AnotherJohnH/picoX7/Source/DX7/OpsAlg6.h

//------------------------------------------------------------------------------
// The data in this file is a derivative of data reverse engineered from die
// photographs of the YM21280 published in Ken Shirriff's blog. That publicly
// available document does not contain a copyright notice or any mention of
// permissions or restrictions that apply to the use of the data. However,
// according to law that does not necessarily mean that the data is free from
// restrictions on its use. At the time of publication, the copyright holder
// is probably Yamaha. If the copyright holder wishes to retrospectively declare
// reasonable and legal restrictions on the data, then either those restrictions
// must be obeyed or this file shouled be deleted.
//
// The statements above shall be included in all copies or substantial portions
// of the data.
//
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
// \brief OPS YM21280 Algorithm
//
// Credit to Ken Shirriff for his decode of the algorithm ROM in the YM21280
// via decapping and die photography

#pragma once

#include "Ops.h"

namespace DX {

//! Implement the 32 DX7 OP algorithms in the YM21280 OPS
template <typename EG_TYPE>
class OpsAlg6 : public Ops</* NUM_OP */ 6, EG_TYPE>
{
public:
   OpsAlg6() = default;

   //! Return next sample for the selected algorithm
   int32_t operator()()
   {
      return (this->*alg_ptr)();
   }

   //! Set the algorithm
   void setOpsAlg(uint8_t algorithm)
   {
      switch (algorithm + 1)
      {
      case  1: alg_ptr = &OpsAlg6::alg1;  break;
      case  2: alg_ptr = &OpsAlg6::alg2;  break;
      case  3: alg_ptr = &OpsAlg6::alg3;  break;
      case  4: alg_ptr = &OpsAlg6::alg4;  break;
      case  5: alg_ptr = &OpsAlg6::alg5;  break;
      case  6: alg_ptr = &OpsAlg6::alg6;  break;
      case  7: alg_ptr = &OpsAlg6::alg7;  break;
      case  8: alg_ptr = &OpsAlg6::alg8;  break;
      case  9: alg_ptr = &OpsAlg6::alg9;  break;
      case 10: alg_ptr = &OpsAlg6::alg10; break;
      case 11: alg_ptr = &OpsAlg6::alg11; break;
      case 12: alg_ptr = &OpsAlg6::alg12; break;
      case 13: alg_ptr = &OpsAlg6::alg13; break;
      case 14: alg_ptr = &OpsAlg6::alg14; break;
      case 15: alg_ptr = &OpsAlg6::alg15; break;
      case 16: alg_ptr = &OpsAlg6::alg16; break;
      case 17: alg_ptr = &OpsAlg6::alg17; break;
      case 18: alg_ptr = &OpsAlg6::alg18; break;
      case 19: alg_ptr = &OpsAlg6::alg19; break;
      case 20: alg_ptr = &OpsAlg6::alg20; break;
      case 21: alg_ptr = &OpsAlg6::alg21; break;
      case 22: alg_ptr = &OpsAlg6::alg22; break;
      case 23: alg_ptr = &OpsAlg6::alg23; break;
      case 24: alg_ptr = &OpsAlg6::alg24; break;
      case 25: alg_ptr = &OpsAlg6::alg25; break;
      case 26: alg_ptr = &OpsAlg6::alg26; break;
      case 27: alg_ptr = &OpsAlg6::alg27; break;
      case 28: alg_ptr = &OpsAlg6::alg28; break;
      case 29: alg_ptr = &OpsAlg6::alg29; break;
      case 30: alg_ptr = &OpsAlg6::alg30; break;
      case 31: alg_ptr = &OpsAlg6::alg31; break;
      case 32: alg_ptr = &OpsAlg6::alg32; break;
      }
   }

private:
   int32_t alg1()
   {
      (void) this->template ops<6, /* SEL */ 1, /* A */ 1, /* C */ 0, /* D */ 0, /* LOG2_COM */ 0b00000>();
      (void) this->template ops<5, /* SEL */ 1, /* A */ 0, /* C */ 0, /* D */ 0, /* LOG2_COM */ 0b00000>();
      (void) this->template ops<4, /* SEL */ 1, /* A */ 0, /* C */ 0, /* D */ 0, /* LOG2_COM */ 0b00000>();
      (void) this->template ops<3, /* SEL */ 0, /* A */ 0, /* C */ 0, /* D */ 1, /* LOG2_COM */ 0b01000>();
      (void) this->template ops<2, /* SEL */ 1, /* A */ 0, /* C */ 1, /* D */ 0, /* LOG2_COM */ 0b00000>();
      return this->template ops<1, /* SEL */ 5, /* A */ 0, /* C */ 1, /* D */ 1, /* LOG2_COM */ 0b01000>();
   }

   int32_t alg2()
   {
      (void) this->template ops<6, /* SEL */ 1, /* A */ 0, /* C */ 0, /* D */ 0, /* LOG2_COM */ 0b00000>();
      (void) this->template ops<5, /* SEL */ 1, /* A */ 0, /* C */ 0, /* D */ 0, /* LOG2_COM */ 0b00000>();
      (void) this->template ops<4, /* SEL */ 1, /* A */ 0, /* C */ 0, /* D */ 0, /* LOG2_COM */ 0b00000>();
      (void) this->template ops<3, /* SEL */ 5, /* A */ 0, /* C */ 0, /* D */ 1, /* LOG2_COM */ 0b01000>();
      (void) this->template ops<2, /* SEL */ 1, /* A */ 1, /* C */ 1, /* D */ 0, /* LOG2_COM */ 0b00000>();
      return this->template ops<1, /* SEL */ 0, /* A */ 0, /* C */ 1, /* D */ 1, /* LOG2_COM */ 0b01000>();
   }

   int32_t alg3()
   {
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
      (void) this->template ops<2, /* SEL */ 0, /* A */ 0, /* C */ 1, /* D */ 1, /* LOG2_COM */ 0b10101>();
      return this->template ops<1, /* SEL */ 5, /* A */ 0, /* C */ 1, /* D */ 1, /* LOG2_COM */ 0b10101>();
   }

   int32_t (OpsAlg6::*alg_ptr)() {&OpsAlg6::alg1};
};

} // namespace DX
