AnotherJohnH/picoX7/Source/DX7/DX7Firmware.h

//------------------------------------------------------------------------------
// The data in this file is a derivative of data reverse engineered from the
// DX7 firmware ROM published on AJXS github project. That publicly
// available project does not contain a copyright notice or any mention of
// permissions or restrictions that apply to the use of the data. However,
// according to law that does not necessarily mean that the data is free from
// restrictions on its use. At the time of publication, the copyright holder
// is probably Yamaha. If the copyright holder wishes to retrospectively declare
// reasonable and legal restrictions on the data, then either those restrictions
// must be obeyed or this file shouled be deleted.
//
// The statements above shall be included in all copies or substantial portions
// of the data.
//
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
// \brief DX7 firmware simulation
//
// Credit to AJXS for his excellent disassembly of the DX7 firmware ROM

#pragma once

#include "Egs.h"

#include "Lfo.h"
#include "Modulation.h"
#include "PitchEg.h"

namespace DX7 {

//! Model of Yamaha DX7 firmware
class Firmware
{
public:
   Firmware(Egs& hw_)
      : hw(hw_)
   {
   }

   //! Load voice patch
   void loadVoice(const SysEx::Voice* patch_)
   {
      voice_patch = *patch_;

      for(unsigned i = 0; i < SysEx::NUM_OP; i++)
      {
         const SysEx::Op& op = voice_patch.op[i];

         patchActivateOperatorEgRate(i, op);
         patchActivateOperatorEgLevel(i, op);
         patchActivateOperatorKbdScaling(i, op);
         patchActivateOperatorKbdVelSens(i, op);
         patchActivateOperatorPitch(i, op);
         patchActivateOperatorKbdRateScaling(i, op);
         patchActivateOperatorDetune(i, op);

         op_enable[i] = (patch_->operator_on & (1 << i)) != 0;
      }

      pitch_eg.load(voice_patch);
      patchActivateAlgMode();
      lfo.load(voice_patch);
   }

   //! Load param patch
   void loadParam(const SysEx::Param* patch_)
   {
      param_patch = *patch_;

      modulation.load(param_patch);
   }

   //! Implement HANDLER_OCF should be called 375 Hz
   void tick()
   {
      lfo.tick();

      computeAmplitudeModulation();

      if (pitch_eg.tick())
      {
         voiceAddLoadFreqToEgs(key_pitch);
      }

      computePitchModulation();

      hw.sendEgsFreq();
   }

   //! Implement VOICE_ADD called for a note on event
   void voiceAdd(uint8_t note_, uint8_t midi_velocity_)
   {
      static const uint8_t table_midi_vel[32] =
      {
         0x6E, 0x64, 0x5A, 0x55, 0x50, 0x4B, 0x46, 0x41,
         0x3A, 0x36, 0x32, 0x2E, 0x2A, 0x26, 0x22, 0x1E,
         0x1C, 0x1A, 0x18, 0x16, 0x14, 0x12, 0x10, 0x0E,
         0x0C, 0x0A, 0x08, 0x06, 0x04, 0x02, 0x01, 0x00
      };

      uint8_t velocity = table_midi_vel[midi_velocity_ >> 2];

      uint8_t note = note_ + voice_patch.transpose - 24;
      if (note > 127)
         note = 127;

      key_pitch = voiceConvertNoteToLogFreq(note);

      voiceAddLoadOperatorDataToEgs(key_pitch, velocity);

      voiceAddLoadFreqToEgs(key_pitch);

      lfo.keyOn();
      pitch_eg.keyOn(/* voice */ 0);

      hw.sendEgsFreq();
      hw.keyOn();
   }

   //! Implement VOICE_REMOVE called for a note off event
   void voiceRemove()
   {
      pitch_eg.keyOff(/* voice */ 0);
      hw.keyOff();
   }

   //! Implement PITCH_BEND_PARSE
   void setPitchBend(int16_t raw14_) { pitch_bend = raw14_; }

   //! Set raw modulation input
   void setModWheel(        uint8_t raw_) { modulation.rawInput(Modulation::MOD_WHEEL,      raw_); }
   void setModFootControl(  uint8_t raw_) { modulation.rawInput(Modulation::FOOT_CONTROL,   raw_); }
   void setModBreathControl(uint8_t raw_) { modulation.rawInput(Modulation::BREATH_CONTROL, raw_); }
   void setModAfterTouch(   uint8_t raw_) { modulation.rawInput(Modulation::AFTER_TOUCH,    raw_); }

private:
   //! Implement PATCH_ACTIVATE_OPERATOR_EG_RATE
   void patchActivateOperatorEgRate(unsigned op_index_, const SysEx::Op& op_)
   {
      for(unsigned i = 0; i < 4; ++i)
      {
         uint8_t rate6 = (op_.eg_amp.rate[i] * 164) >> 8;

         hw.op[op_index_].setEgRate(i, rate6);
      }
   }

   //! Implement PATCH_ACTIVATE_OPERATOR_EG_LEVEL
   void patchActivateOperatorEgLevel(unsigned op_index_, const SysEx::Op& op_)
   {
      for(unsigned i = 0; i < 4; ++i)
      {
         uint8_t level6 = table_log[op_.eg_amp.level[i]] >> 1;

         hw.op[op_index_].setEgAtten(i, level6);
      }
   }

   //! Implement PATCH_ACTIVATE_OPERATOR_KBD_SCALING
   void patchActivateOperatorKbdScaling(unsigned index, const SysEx::Op& op)
   {
      unsigned breakpoint  = table_key_pitch[op.kbd_lvl_scl_bpt + 20] >> 2;
      unsigned depth_left  = (op.kbd_lvl_scl_lft_depth * 660) >> 8;
      unsigned depth_right = (op.kbd_lvl_scl_rgt_depth * 660) >> 8;

      static const uint8_t table_kbd_scaling_curve_exp[36] =
      {
         0x00, 0x01, 0x02, 0x03, 0x04, 0x05,
         0x06, 0x07, 0x08, 0x09, 0x0B, 0x0E,
         0x10, 0x13, 0x17, 0x1C, 0x21, 0x27,
         0x2F, 0x39, 0x43, 0x50, 0x5F, 0x71,
         0x86, 0xA0, 0xBE, 0xE0, 0xFF, 0xFF,
         0xFF, 0xFF, 0xFF, 0xFF, 0xFF, 0xFF
      };

      static const uint8_t table_kbd_scaling_curve_lin[36] =
      {
         0x00, 0x08, 0x10, 0x18, 0x20, 0x28,
         0x30, 0x38, 0x40, 0x48, 0x50, 0x58,
         0x60, 0x68, 0x70, 0x78, 0x80, 0x88,
         0x90, 0x98, 0xA0, 0xA8, 0xB2, 0xB8,
         0xC0, 0xC8, 0xD0, 0xD8, 0xE0, 0xE8,
         0xF0, 0xF8, 0xFF, 0xFF, 0xFF, 0xFF
      };

      // Note, sign is "opposite" as lower values are louder

      signed         left_sign  = op.kbd_lvl_scl_lft_curve >= 2 ? -1 : +1;
      bool           left_lin   = op.kbd_lvl_scl_lft_curve == 0 || op.kbd_lvl_scl_lft_curve == 3;
      const uint8_t* left_curve = left_lin ? table_kbd_scaling_curve_lin
                                           : table_kbd_scaling_curve_exp;

      signed         right_sign  = op.kbd_lvl_scl_rgt_curve >= 2 ? -1 : +1;
      bool           right_lin   = op.kbd_lvl_scl_rgt_curve == 0 || op.kbd_lvl_scl_rgt_curve == 3;
      const uint8_t* right_curve = right_lin ? table_kbd_scaling_curve_lin
                                             : table_kbd_scaling_curve_exp;

      unsigned out_level = table_log[op.out_level];

      for(signed note = 1; note <= 43; ++note)
      {
         signed offset = note - breakpoint;

         signed curve = offset <= 0 ? left_curve[-offset] * depth_left * left_sign
                                    : right_curve[offset] * depth_right * right_sign;

         signed note_level = (out_level + (curve >> 8)) << 1;

         if (note_level < 0)
            note_level = 0;
         else if (note_level > 0xFF)
            note_level = 0xFF;

         operator_keyboard_scaling[index][note - 1] = note_level;
      }
   }

   //! Implement PATCH_ACTIVATE_OPERATOR_VEL_SENS
   void patchActivateOperatorKbdVelSens(unsigned index, const SysEx::Op& op)
   {
      patch_op_sens[index] = (8 - op.key_vel_sense) * 0x1E0;
   }

   //! Implement PATCH_ACTIVATE_OPERATOR_PITCH
   void patchActivateOperatorPitch(unsigned index, const SysEx::Op& op)
   {
      if (op.osc_mode == SysEx::RATIO)
      {
         const uint16_t table_op_freq_coarse[32] =
         {
            0xF000, 0x0000, 0x1000, 0x195C, 0x2000, 0x2528, 0x295C, 0x2CEC,
            0x3000, 0x32B8, 0x3528, 0x375A, 0x395C, 0x3B34, 0x3CEC, 0x3E84,
            0x4000, 0x4168, 0x42B8, 0x43F8, 0x4528, 0x4648, 0x475A, 0x4860,
            0x495C, 0x4A4C, 0x4B34, 0x4C14, 0x4CEC, 0x4DBA, 0x4E84, 0x4F44
         };

         const uint16_t table_op_freq_fine[100] =
         {
            0x000, 0x03A, 0x075, 0x0AE, 0x0E7, 0x120, 0x158, 0x18F, 0x1C6, 0x1FD,
            0x233, 0x268, 0x29D, 0x2D2, 0x306, 0x339, 0x36D, 0x39F, 0x3D2, 0x403,
            0x435, 0x466, 0x497, 0x4C7, 0x4F7, 0x526, 0x555, 0x584, 0x5B2, 0x5E0,
            0x60E, 0x63B, 0x668, 0x695, 0x6C1, 0x6ED, 0x719, 0x744, 0x76F, 0x799,
            0x7C4, 0x7EE, 0x818, 0x841, 0x86A, 0x893, 0x8BC, 0x8E4, 0x90C, 0x934,
            0x95C, 0x983, 0x9AA, 0x9D1, 0x9F7, 0xA1D, 0xA43, 0xA69, 0xA8F, 0xAB4,
            0xAD9, 0xAFE, 0xB22, 0xB47, 0xB6B, 0xB8F, 0xBB2, 0xBD6, 0xBF9, 0xC1C,
            0xC3F, 0xC62, 0xC84, 0xCA7, 0xCC9, 0xCEA, 0xD0C, 0xD2E, 0xD4F, 0xD70,
            0xD91, 0xDB2, 0xDD2, 0xDF3, 0xE13, 0xE33, 0xE53, 0xE72, 0xE92, 0xEB1,
            0xED0, 0xEEF, 0xF0E, 0xF2D, 0xF4C, 0xF6A, 0xF88, 0xFA6, 0xFC4, 0xFE2
         };

         hw.op[index].setPitchFixed(false);

         hw.op[index].setPitchRatio(table_op_freq_coarse[op.osc_freq_coarse] +
                                    table_op_freq_fine[op.osc_freq_fine] +
                                    0x232C);
      }
      else
      {
         const uint16_t table_op_freq_fixed[4] =
         {
            0x0000, 0x3526, 0x6A4C, 0x9F74
         };

         hw.op[index].setPitchFixed(true);

         hw.op[index].setPitchRatio(table_op_freq_fixed[op.osc_freq_coarse & 0b11] +
                                    op.osc_freq_fine * 136 +
                                    0x16AC);
      }
   }

   //! Implement PATCH_ACTIVATE_OPERATOR_KBD_RATE_SCALING
   void patchActivateOperatorKbdRateScaling(unsigned index, const SysEx::Op& op)
   {
      hw.op[index].setEgRateScale(op.kbd_rate_scale);
      hw.op[index].setAmpModSens(op.amp_mod_sense);
   }

   //! Implement PATCH_ACTIVATE_OPERATOR_DETUNE
   void patchActivateOperatorDetune(unsigned index, const SysEx::Op& op)
   {
      hw.op[index].setDetune(op.osc_detune - 7);
   }

   //! Implement PATCH_ACTIVATE_ALG_MODE
   void patchActivateAlgMode()
   {
      hw.setOpsSync(voice_patch.osc_sync);
      hw.setOpsAlg(voice_patch.alg);
      hw.setOpsFdbk(voice_patch.feedback);
   }

   //! Implement VOICE_CONVERT_NOTE_TO_LOG_FREQ
   uint16_t voiceConvertNoteToLogFreq(uint8_t note_)
   {
      uint8_t value   = table_key_pitch[note_];
      uint8_t ls_bits = value & 0b11;
      return (value << 8) | (ls_bits << 6) | (ls_bits << 4) | (ls_bits << 2);
   }

   //! Implement VOICE_ADD_LOAD_OPERATOR_DATA_TO_EGS
   void voiceAddLoadOperatorDataToEgs(uint16_t pitch_, uint8_t note_vel7_)
   {
      static uint8_t table_op_volume_velocity_scale[32] =
      {
         0x00, 0x04, 0x0C, 0x15, 0x1E, 0x28, 0x2E, 0x34,
         0x3A, 0x40, 0x46, 0x4C, 0x52, 0x58, 0x5E, 0x64,
         0x67, 0x6A, 0x6D, 0x70, 0x72, 0x74, 0x76, 0x78,
         0x7A, 0x7C, 0x7E, 0x80, 0x82, 0x83, 0x84, 0x85
      };

      uint8_t scale = table_op_volume_velocity_scale[note_vel7_ >> 2];

      for(unsigned op_index = 0; op_index < SysEx::NUM_OP; ++op_index)
      {
         uint16_t vel_sense = patch_op_sens[op_index];

         unsigned vol = ((vel_sense & 0xFF00) + scale * (vel_sense & 0xFF)) >> 8;
         if (vol > 0xFF) vol = 0xFF;

         op_volume[op_index] = vol;

         if (not op_enable[op_index])
         {
            vol = 0xFF;
         }
         else
         {
            vol = op_volume[op_index] + operator_keyboard_scaling[op_index][pitch_ >> 10];

            if (vol > 0xFF)
            {
               vol = 0xFF;
            }
            else if (vol < 4)
            {
               vol = 4;
            }
         }

         hw.op[op_index].setOpAtten(vol);
      }
   }

   //! Implement VOICE_ADD_LOAD_FREQ_TO_EGS
   void voiceAddLoadFreqToEgs(signed pitch_)
   {
      pitch_ += pitch_eg.getOutput(/* voice */ 0);

      pitch_ -= 0x1BA8;
      if (pitch_ < 0)
         pitch_ = 0;

      pitch_ += master_tune;

      hw.setEgsVoicePitch(pitch_);
   }

   void computeAmplitudeModulation()
   {
      unsigned mod = lfo.getAmpMod() + modulation.getAmpMod();
      if (mod > 0xFF) mod = 0xFF;

      mod += modulation.getEGBias();
      if (mod > 0xFF) mod = 0xFF;
      mod -= modulation.getEGBias();

      uint8_t value = (mod * (~lfo.getAmpOutput() ^ 0x80)) >> 8;
      value += modulation.getEGBias();
      if (value > 0xFF) value = 0xFF;

      static uint8_t table_amp_mod[256] =
      {
         0xFF, 0xFF, 0xE0, 0xCD, 0xC0, 0xB5, 0xAD, 0xA6, 0xA0, 0x9A, 0x95, 0x91, 0x8D, 0x89, 0x86, 0x82,
         0x80, 0x7D, 0x7A, 0x78, 0x75, 0x73, 0x71, 0x6F, 0x6D, 0x6B, 0x69, 0x67, 0x66, 0x64, 0x62, 0x61,
         0x60, 0x5E, 0x5D, 0x5B, 0x5A, 0x59, 0x58, 0x56, 0x55, 0x54, 0x53, 0x52, 0x51, 0x50, 0x4F, 0x4E,
         0x4D, 0x4C, 0x4B, 0x4A, 0x49, 0x48, 0x47, 0x46, 0x46, 0x45, 0x44, 0x43, 0x42, 0x42, 0x41, 0x40,
         0x40, 0x3F, 0x3E, 0x3D, 0x3D, 0x3C, 0x3B, 0x3B, 0x3A, 0x39, 0x39, 0x38, 0x38, 0x37, 0x36, 0x36,
         0x35, 0x35, 0x34, 0x33, 0x33, 0x32, 0x32, 0x31, 0x31, 0x30, 0x30, 0x2F, 0x2F, 0x2E, 0x2E, 0x2D,
         0x2D, 0x2C, 0x2C, 0x2B, 0x2B, 0x2A, 0x2A, 0x2A, 0x29, 0x29, 0x28, 0x28, 0x27, 0x27, 0x26, 0x26,
         0x26, 0x25, 0x25, 0x24, 0x24, 0x24, 0x23, 0x23, 0x22, 0x22, 0x22, 0x21, 0x21, 0x21, 0x20, 0x20,
         0x20, 0x1F, 0x1F, 0x1E, 0x1E, 0x1E, 0x1D, 0x1D, 0x1D, 0x1C, 0x1C, 0x1C, 0x1B, 0x1B, 0x1B, 0x1A,
         0x1A, 0x1A, 0x19, 0x19, 0x19, 0x18, 0x18, 0x18, 0x18, 0x17, 0x17, 0x17, 0x16, 0x16, 0x16, 0x15,
         0x15, 0x15, 0x15, 0x14, 0x14, 0x14, 0x13, 0x13, 0x13, 0x13, 0x12, 0x12, 0x12, 0x12, 0x11, 0x11,
         0x11, 0x11, 0x10, 0x10, 0x10, 0x10, 0x0F, 0x0F, 0x0F, 0x0F, 0x0E, 0x0E, 0x0E, 0x0E, 0x0D, 0x0D,
         0x0D, 0x0D, 0x0C, 0x0C, 0x0C, 0x0C, 0x0B, 0x0B, 0x0B, 0x0B, 0x0A, 0x0A, 0x0A, 0x0A, 0x09, 0x09,
         0x09, 0x09, 0x08, 0x08, 0x08, 0x08, 0x08, 0x07, 0x07, 0x07, 0x07, 0x06, 0x06, 0x06, 0x06, 0x06,
         0x05, 0x05, 0x05, 0x05, 0x05, 0x04, 0x04, 0x04, 0x04, 0x04, 0x03, 0x03, 0x03, 0x03, 0x03, 0x02,
         0x02, 0x02, 0x02, 0x02, 0x02, 0x01, 0x01, 0x01, 0x01, 0x01, 0x00, 0x00, 0x00, 0x00, 0x00, 0x00
      };

      hw.setEgsAmpMod(table_amp_mod[uint8_t(~value)]);
   }

   void computePitchModulation()
   {
      unsigned mod = lfo.getPitchMod() + modulation.getPitchMod();
      if (mod > 0xFF) mod = 0xFF;

      int16_t value = mod * lfo.getPitchOutput();

      value = (value >> 1) + pitch_bend;

      hw.setEgsPitchMod(value);
   }

   const uint8_t table_log[100] =
   {
      0x7F, 0x7A, 0x76, 0x72, 0x6E, 0x6B, 0x68, 0x66, 0x64, 0x62,
      0x60, 0x5E, 0x5C, 0x5A, 0x58, 0x56, 0x55, 0x54, 0x52, 0x51,
      0x4F, 0x4E, 0x4D, 0x4C, 0x4B, 0x4A, 0x49, 0x48, 0x47, 0x46,
      0x45, 0x44, 0x43, 0x42, 0x41, 0x40, 0x3F, 0x3E, 0x3D, 0x3C,
      0x3B, 0x3A, 0x39, 0x38, 0x37, 0x36, 0x35, 0x34, 0x33, 0x32,
      0x31, 0x30, 0x2F, 0x2E, 0x2D, 0x2C, 0x2B, 0x2A, 0x29, 0x28,
      0x27, 0x26, 0x25, 0x24, 0x23, 0x22, 0x21, 0x20, 0x1F, 0x1E,
      0x1D, 0x1C, 0x1B, 0x1A, 0x19, 0x18, 0x17, 0x16, 0x15, 0x14,
      0x13, 0x12, 0x11, 0x10, 0x0F, 0x0E, 0x0D, 0x0C, 0x0B, 0x0A,
      0x09, 0x08, 0x07, 0x06, 0x05, 0x04, 0x03, 0x02, 0x01, 0x00
   };

   const uint8_t table_key_pitch[128] =
   {
      0x00, 0x00, 0x01, 0x02, 0x04, 0x05, 0x06, 0x08,
      0x09, 0x0A, 0x0C, 0x0D, 0x0E, 0x10, 0x11, 0x12,
      0x14, 0x15, 0x16, 0x18, 0x19, 0x1A, 0x1C, 0x1D,
      0x1E, 0x20, 0x21, 0x22, 0x24, 0x25, 0x26, 0x28,
      0x29, 0x2A, 0x2C, 0x2D, 0x2E, 0x30, 0x31, 0x32,
      0x34, 0x35, 0x36, 0x38, 0x39, 0x3A, 0x3C, 0x3D,
      0x3E, 0x40, 0x41, 0x42, 0x44, 0x45, 0x46, 0x48,
      0x49, 0x4A, 0x4C, 0x4D, 0x4E, 0x50, 0x51, 0x52,
      0x54, 0x55, 0x56, 0x58, 0x59, 0x5A, 0x5C, 0x5D,
      0x5E, 0x60, 0x61, 0x62, 0x64, 0x65, 0x66, 0x68,
      0x69, 0x6A, 0x6C, 0x6D, 0x6E, 0x70, 0x71, 0x72,
      0x74, 0x75, 0x76, 0x78, 0x79, 0x7A, 0x7C, 0x7D,
      0x7E, 0x80, 0x81, 0x82, 0x84, 0x85, 0x86, 0x88,
      0x89, 0x8A, 0x8C, 0x8D, 0x8E, 0x90, 0x91, 0x92,
      0x94, 0x95, 0x96, 0x98, 0x99, 0x9A, 0x9C, 0x9D,
      0x9E, 0xA0, 0xA1, 0xA2, 0xA4, 0xA5, 0xA6, 0xA8
   };

   SysEx::Voice voice_patch;
   SysEx::Param param_patch;

   // Firmware state
#if defined(HW_NATIVE)
   int16_t      master_tune{0x0121}; // Tune up to attempt to compenstate for 48KHz sample rate
#else
   int16_t      master_tune{0x0100};
#endif

   int16_t      pitch_bend;

   Modulation   modulation;
   Lfo          lfo;
   PitchEg<1>   pitch_eg;
   uint16_t     key_pitch;

   uint16_t     patch_op_sens[6];                  //!< M_PATCH_OP_SENS
   uint16_t     op_volume[6];                      //!< M_OP_VOULME
   bool         op_enable[6];
   uint8_t      operator_keyboard_scaling[6][43];  //!< M_OPERATOR_KEYBOARD_SCALING

   // DX7 EGS and OPS interface
   Egs&          hw;
};

} // namespace DX7
