AnotherJohnH/picoX7/Source/DX7/Ops.h

//-------------------------------------------------------------------------------
// Copyright (c) 2023 John D. Haughton
// SPDX-License-Identifier: MIT
//-------------------------------------------------------------------------------

#pragma once

#include "Table_dx_exp_14.h"
#include "Table_dx_exp_32.h"
#include "Table_dx_log_sine_14.h"

//! Model of Yamaha OPS (like the YM21280)
template <unsigned NUM_OP, typename EG_TYPE>
class Ops
{
public:
   Ops() = default;

   EG_TYPE* getEgPointer(unsigned op_index_) { return &state[op_index_].eg; }

   //! Set the oscillator sync mode
   void setOpsSync(bool sync_)
   {
      sync = sync_;
   }

   //! Set the algorithm feedback level
   void setOpsFdbk(uint8_t feedback_)
   {
      fdbk = (7 - feedback_) + 2;
   }

   //! Set operator frequency
   void setOpsFreq(unsigned op_index, uint32_t f14)
   {
      // In the DX7 this lookup table is 14 bits in 22 bits out
      // with some logic to re-use the unusable high end above
      // the nyquist for very low frequencies this logic has
      // been pre-folded into the 14 bits in 32 bits out
      // table used here by the table auto-generation script
      state[op_index].phase_inc_32 = table_dx_exp_32[f14];
   }

   //! Start of note
   void keyOn()
   {
      if (sync)
      {
         for(unsigned op_index = 0; op_index < NUM_OP; ++op_index)
         {
            state[op_index].phase_acc_32 = 0;
         }
      }
   }

protected:
   //! Simulate a single operator
   template <unsigned OP_NUMBER, unsigned SEL, bool A, bool C, bool D, unsigned LOG2_COM>
   int32_t ops()
   {
      // Documented operator number 1..N map to internal operator index N-1..0
      // the internal index follows the order of operator computation
      // and the order of operator parameter encoding in the SysEx patch
      // encoding
      const unsigned op_index = NUM_OP - OP_NUMBER;

      // Sample sine table
      uint32_t phase_32    = state[op_index].stepPhase();
      uint32_t phase_12    = (phase_32 + (modulation_15 << 20)) >> (32 - 12);
      uint32_t log_wave_14 = table_dx_log_sine_14[phase_12];

      // Apply EG attenuation
      log_wave_14 += state[op_index].eg.getAtten12() << 2;

      // Apply algorithm compensation
      log_wave_14 += LOG2_COM << 7;

      // Limit to maximum attenuation TODO fold into exp table
      if (log_wave_14 > 0x3FFF)
         log_wave_14 = 0x3FFF;

      // Convert log sample to linear
      signed output_15 = table_dx_exp_14[log_wave_14];
      if (phase_12 >= 0x800)
         output_15 = -output_15;

      // Mixing and routing as required by the algorithm
      signed sum_15 = 0;
      if (C) sum_15 = memory_15;
      if (D) sum_15 += output_15;

      switch(SEL)
      {
      case 0: modulation_15 = 0;                                     break;
      case 1: modulation_15 = output_15;                             break;
      case 2: modulation_15 = sum_15;                                break;
      case 3: modulation_15 = memory_15;                             break;
      case 4: modulation_15 = feedback1_15;                          break;
      case 5: modulation_15 = (feedback1_15 + feedback2_15) >> fdbk; break;
      }

      if (A)
      {
         // Feeedback path enabled
         feedback2_15 = feedback1_15;
         feedback1_15 = output_15;
      }

      if (C or D)
      {
         // Memory write enable
         memory_15 = sum_15;
      }

      // 16-bit sample returned and only used from the final operator
      return sum_15 << 1;
   }

private:
   // Externaly configured state
   bool    sync{true};
   uint8_t fdbk{0};

   // Internal voice computation state
   int32_t modulation_15{0};
   int32_t feedback1_15{0};
   int32_t feedback2_15{0};
   int32_t memory_15{0};

   // Internal operator state
   struct State
   {
      EG_TYPE  eg{};
      uint32_t phase_acc_32{0};
      uint32_t phase_inc_32{0};

      uint32_t stepPhase()
      {
         phase_acc_32 += phase_inc_32;
         return phase_acc_32;
      }
   };

   State state[NUM_OP];
};
