AnotherJohnH/picoX7/Source/DX7/EgsOps.h

//------------------------------------------------------------------------------
// Copyright (c) 2023 John D. Haughton
//
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
#pragma once

#include "VoiceBase.h"

#include "Table_dx7_sine_15.h"
#include "Table_dx7_sine_div3_15.h"
#include "Table_dx7_sine_div5_15.h"

#include "EnvGen.h"

//! Model of Yamaha OPS and EGS
template <unsigned NUM_OP>
class EgsOps
{
public:
   EgsOps() = default;

   //! Check if all amplitude envelopes are at L4
   //! NOTE: This is not functionality performed by a real DX
   bool isComplete() const
   {
      for(unsigned i = 0; i < NUM_OP; ++i)
      {
         if (not egs[i].isComplete())
            return false;
      }

      return true;
   }

   //! Re-program voice from SysEx
   void prog(const SysEx::Voice* sysex)
   {
      for(unsigned i = 0; i < NUM_OP; i++)
      {
         const SysEx::Op& op = sysex->op[5 - i];

         egs[i].prog(op.eg_amp, op.out_level);
      }

      fbl     = (7 - sysex->feedback) + 4;
      op_sync = sysex->osc_sync;
   }

   //! Start of note
   void keyOn()
   {
      for(unsigned i = 0; i < NUM_OP; ++i)
      {
         if (op_sync)
         {
            phase_accum_32[i] = 0;
         }

         egs[i].gateOn();
      }
   }

   //! Release of note
   void keyOff()
   {
      for(unsigned i = 0; i < NUM_OP; ++i)
      {
         egs[i].gateOff();
      }
   }

   //! Set operator frequency
   void setFreq(unsigned i, uint32_t f14)
   {
      phase_inc_32[i] = f14;
   }

protected:
   //! Simulate a single operator (and associated envelope generator)
   template <unsigned OP, unsigned SEL, bool A, bool C, bool D, unsigned COM>
   int32_t ops()
   {
      const unsigned i = OP - 1;

      int32_t amp_14 = egs[i]();

      phase_accum_32[i] += phase_inc_32[i];

      uint32_t phase_12 = (phase_accum_32[i] + (modulation_12 << 22)) >> 20;

      int32_t output_15;
      switch (COM)
      {
      case 1: output_15 = (table_dx7_sine_15[phase_12]      * amp_14) >> 14; break; //  1/1
      case 2: output_15 = (table_dx7_sine_15[phase_12]      * amp_14) >> 15; break; //  1/2
      case 3: output_15 = (table_dx7_sine_div3_15[phase_12] * amp_14) >> 14; break; //  1/3
      case 4: output_15 = (table_dx7_sine_15[phase_12]      * amp_14) >> 16; break; //  1/4
      case 5: output_15 = (table_dx7_sine_div5_15[phase_12] * amp_14) >> 14; break; //  1/5
      case 6: output_15 = (table_dx7_sine_div3_15[phase_12] * amp_14) >> 15; break; //  1/6
      }

      int32_t sum_15 = 0;
      if (C) sum_15 = memory_15;
      if (D) sum_15 += output_15;

      switch(SEL)
      {
      case 0: modulation_12 = 0;                                    break;
      case 1: modulation_12 = output_15 >> 3;                       break;
      case 2: modulation_12 = sum_15 >> 3;                          break;
      case 3: modulation_12 = memory_15 >> 3;                       break;
      case 4: modulation_12 = feedback1_15 >> 3;                    break;
      case 5: modulation_12 = (feedback1_15 + feedback2_15) >> fbl; break;
      }

      if (A)
      {
         // Feeedback path enabled
         feedback2_15 = feedback1_15;
         feedback1_15 = output_15;
      }

      if (C or D)
      {
         // Memory write enable
         memory_15 = sum_15;
      }

      return sum_15 << 1;
   }

private:
   // OPS state
   uint8_t  fbl {0};
   bool     op_sync {true};

   uint32_t phase_accum_32[NUM_OP] = {0};
   uint32_t phase_inc_32[NUM_OP]   = {0};

   int32_t  modulation_12 {0};
   int32_t  feedback1_15 {0};
   int32_t  feedback2_15 {0};
   int32_t  memory_15 {0};

   // EGS state
   EnvGen   egs[NUM_OP];
};
